edward62740/WMNS/Software Files/nrf_firmware/docu/meshnetwork.jpg

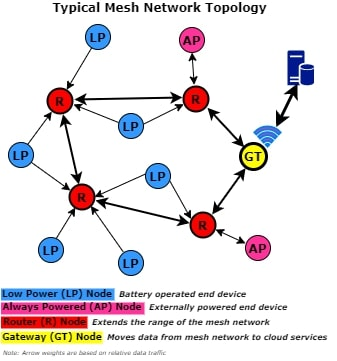
Software Files/nrf_firmware/docu/meshnetwork.jpg
