edward62740/WMNS/PCB Files/Debugger/Debugger.brd

## EAGLE design PCB Files/Debugger/Debugger.brd (2022-01-03)

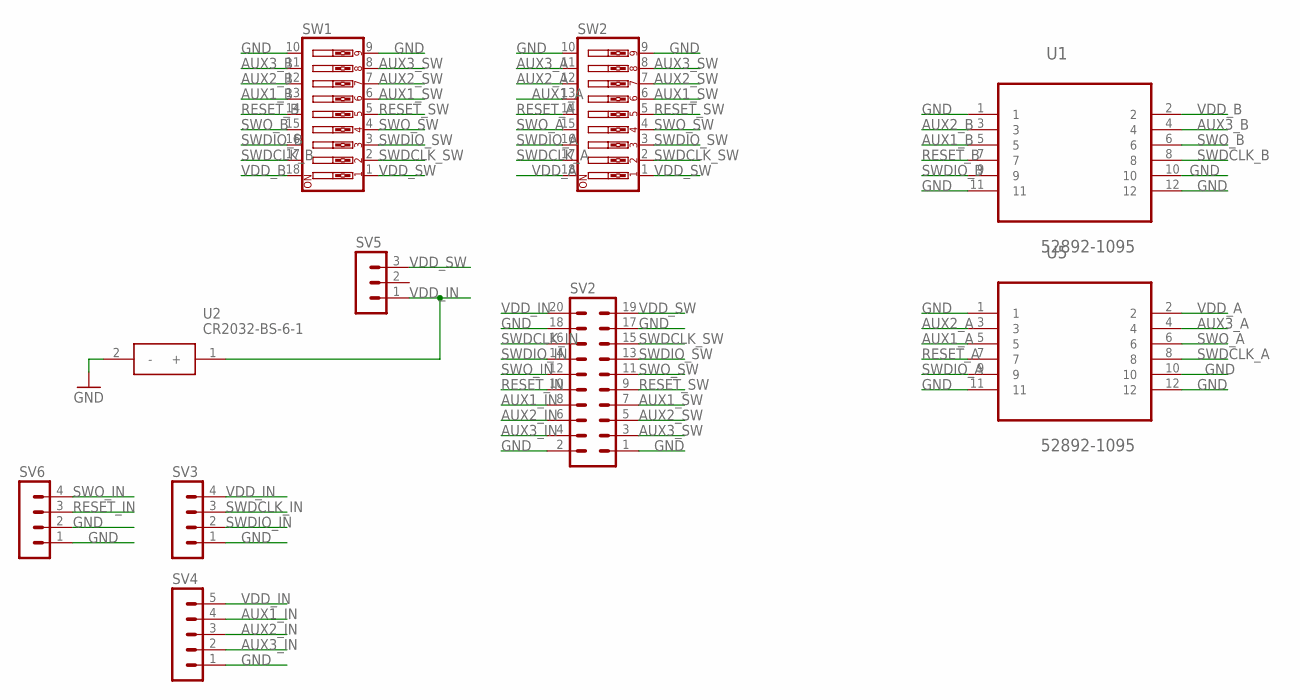
[picture p53: schematic Debugger.sch]

Parts:
SV2: MA10-2
SV3, SV6: MA04-1
SV4: MA05-1
SV5: MA03-1
SW1, SW2: SW_DIP-9; EDG-09
U1, U5: 52892-1095; MOLEX_52892-1095
U2: CR2032-BS-6-1; CR2032BS61

Connections:
AUX1_A: SW2.13, U5.5
AUX1_B: SW1.13, U1.5
AUX1_IN: SV2.8, SV4.4
AUX1_SW: SV2.7, SW1.6, SW2.6
AUX2_A: SW2.12, U5.3
AUX2_B: SW1.12, U1.3
AUX2_IN: SV2.6, SV4.3
AUX2_SW: SV2.5, SW1.7, SW2.7
AUX3_A: SW2.11, U5.4
AUX3_B: SW1.11, U1.4
AUX3_IN: SV2.4, SV4.2
AUX3_SW: SV2.3, SW1.8, SW2.8
GND: SV2.1, SV2.2, SV2.17, SV2.18, SV3.1, SV4.1, SV6.1, SV6.2, SW1.9, SW1.10, SW2.9, SW2.10, U1.1, U1.10, U1.11, U1.12, U2.2 (-), U5.1, U5.10, U5.11, U5.12
RESET_A: SW2.14, U5.7
RESET_B: SW1.14, U1.7
RESET_IN: SV2.10, SV6.3
RESET_SW: SV2.9, SW1.5, SW2.5
SWDCLK_A: SW2.17, U5.8
SWDCLK_B: SW1.17, U1.8
SWDCLK_IN: SV2.16, SV3.3
SWDCLK_SW: SV2.15, SW1.2, SW2.2
SWDIO_A: SW2.16, U5.9
SWDIO_B: SW1.16, U1.9
SWDIO_IN: SV2.14, SV3.2
SWDIO_SW: SV2.13, SW1.3, SW2.3
SWO_A: SW2.15, U5.6
SWO_B: SW1.15, U1.6
SWO_IN: SV2.12, SV6.4
SWO_SW: SV2.11, SW1.4, SW2.4
VDD_A: SW2.18, U5.2
VDD_B: SW1.18, U1.2
VDD_IN: SV2.20, SV3.4, SV4.5, SV5.1, U2.1 (+)
VDD_SW: SV2.19, SV5.3, SW1.1, SW2.1

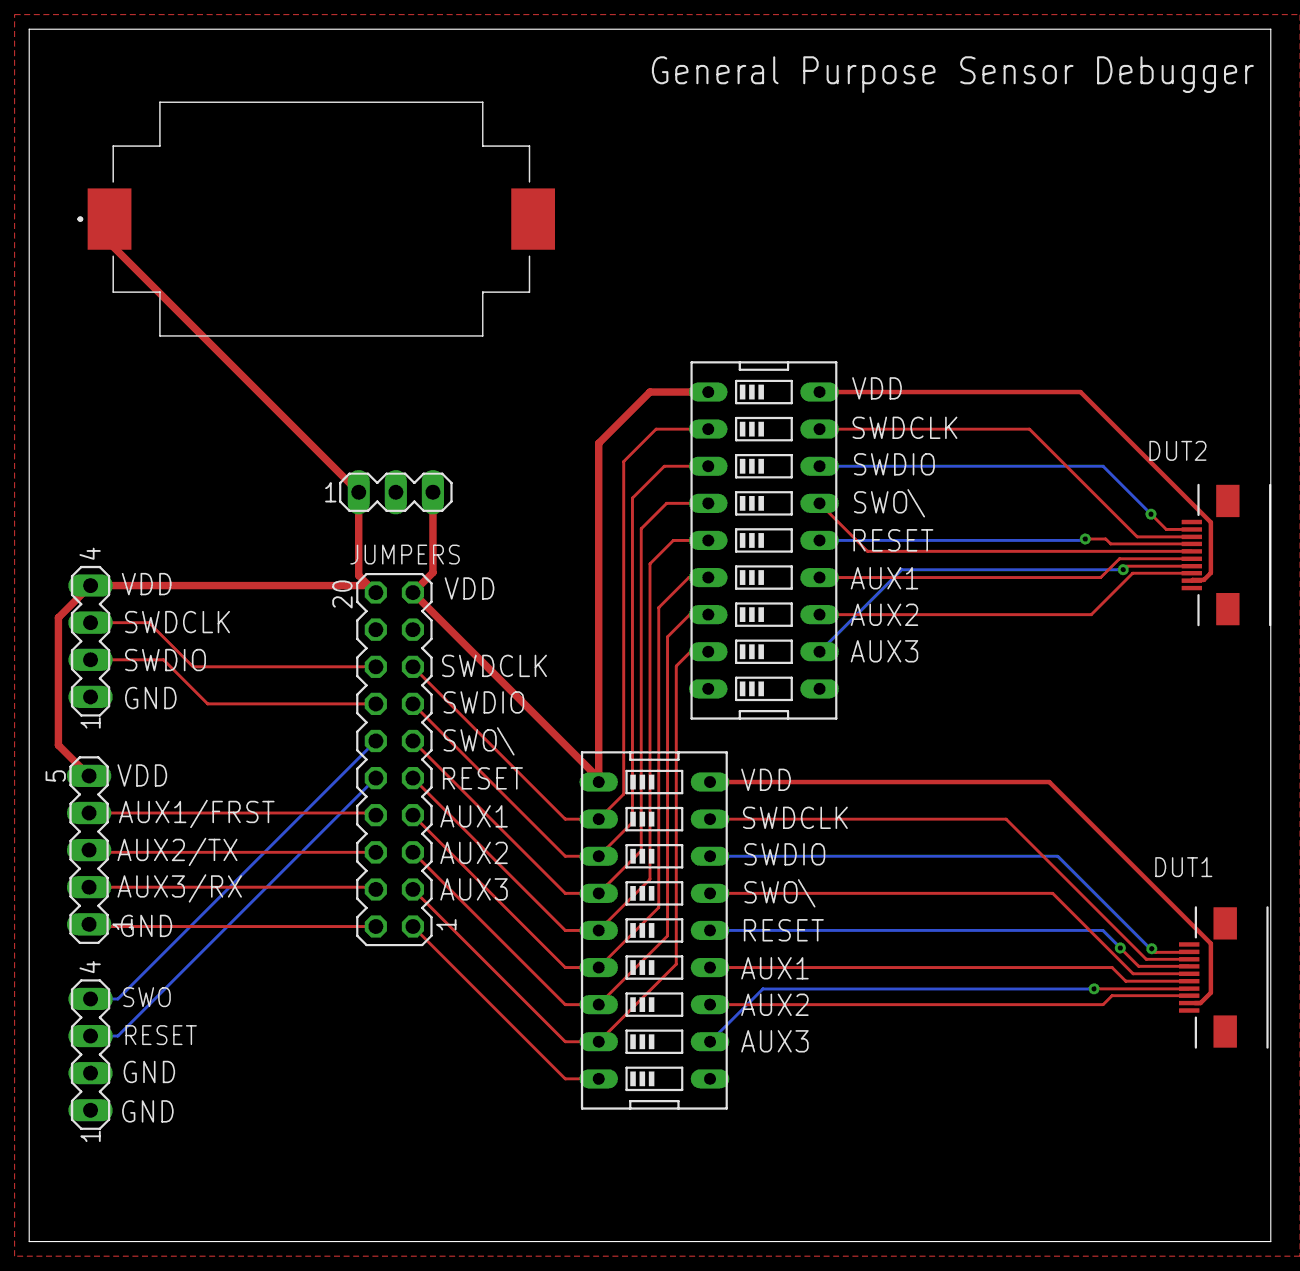
[picture p54: board Debugger.brd from above]

Board: 2 copper layers, 85.0 x 83.0 mm, 10 parts (0 on the bottom side), 33 nets.
