edward62740/WMNS/PCB Files/Gateway/Gateway v2.brd

## EAGLE design PCB Files/Gateway/Gateway v2.brd (2022-01-03)

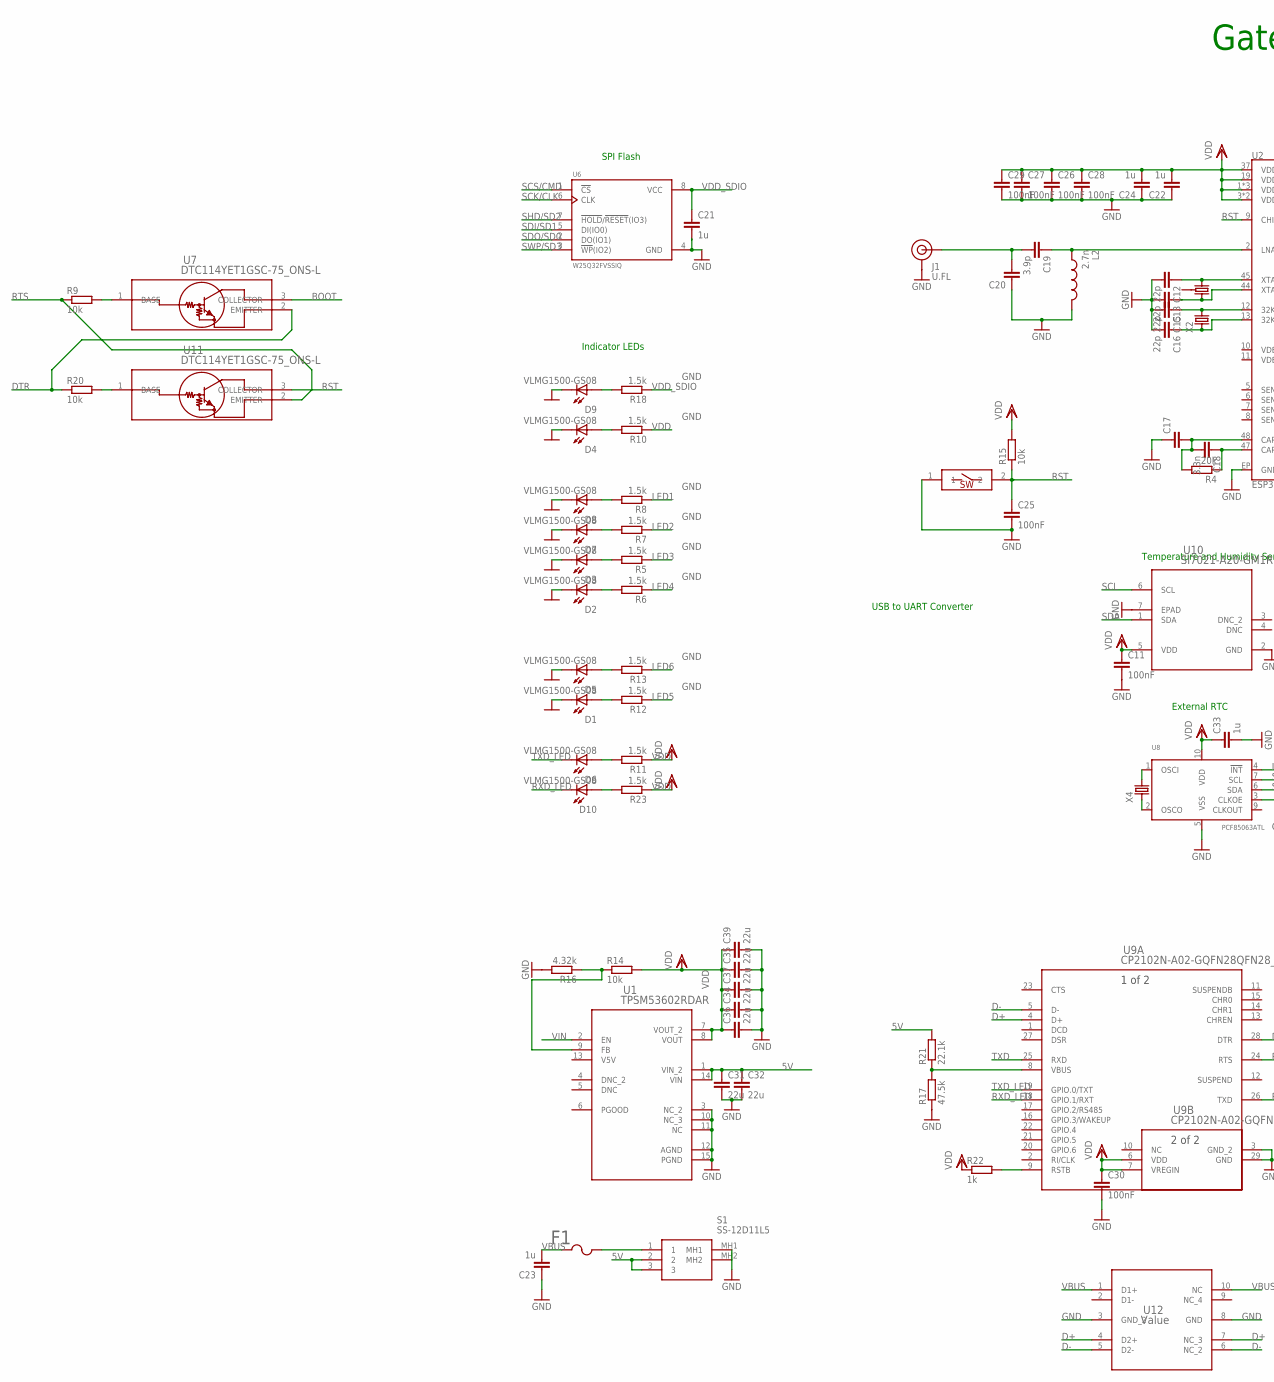
[picture p55: schematic Gateway v2.sch, part in row 1, column 1]

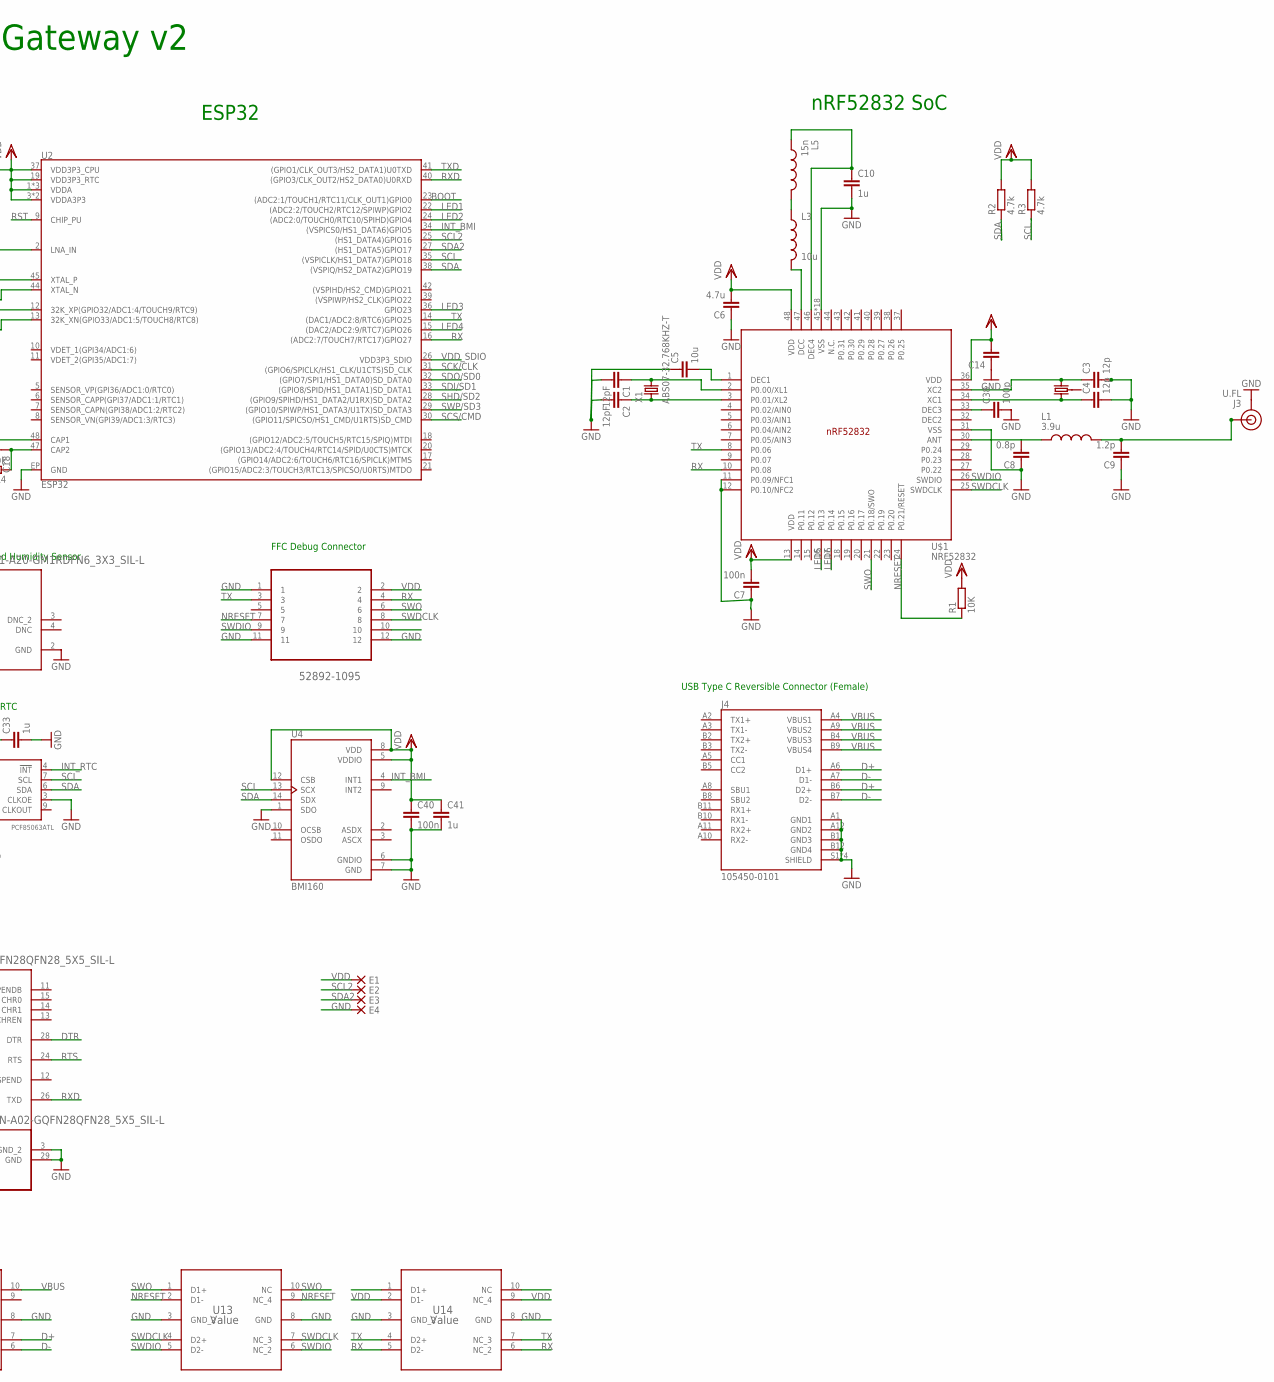
[picture p56: schematic Gateway v2.sch, part in row 1, column 2]

Parts:
C1, C2: 12pF; C0402
C3, C4: 12p; C0402
C5: 10u; C0402
C6: 4.7u; C0402
C7, C40: 100n; C0402
C8: 0.8p; C0402
C9: 1.2p; C0402
C10, C21, C41: 1u; C0402
C11, C25, C26, C27, C28, C29, C30: 100nF; C0402
C12, C13, C15, C16: 22p; C0402
C14: 100u; C0402
C17: 10n; C0402
C18: 3.3n; C0402
C19: 3.9p; C0402
C20: 2.4p; C0402
C22, C23, C24, C33: 1u; C0603R
C31, C32, C34, C35, C36, C37, C39: 22u; C0603R
C38: 100p; C0402
D1, D2, D3, D4, D5, D6, D7, D8, D9, D10: VLMG1500-GS08; LEDC1005X35N
E1, E2, E3, E4: DPADS_PAD-0400-S; DPADS_0400-S
F1: 1210L050YR1210LSERIES_LTF-L; 1210LSERIES_LTF-L
J1, J3: U.FL
J4: 105450-0101; MOLEX_105450-0101
L1: 3.9u; INDC0402X26N
L2: 2.7n; INDC0402X26N
L3: 10u; L0603
L5: 15n; INDC0402X26N
R1: 10K; R0402
R2, R3: 4.7k; R0402
R4: 20k; R0402
R5, R6, R7, R8, R10, R11, R12, R13, R18, R23: 1.5k; R0402
R9, R14, R15, R20: 10k; R0402
R16: 4.32k; R0402
R17: 47.5k; R0402
R21: 22.1k; R0402
R22: 1k; R0402
RESET: SMDSWITCH; RESC4217X170
S1: SS-12D11L5; SS12D11L5
U1: TPSM53602RDAR; B3QFN15_RDA_TEX
U2: ESP32; QFN48-0.4MM
U4: BMI160; PQFN50P300X250X88-14N
U5: 52892-1095; MOLEX_52892-1095
U6: W25Q32FVSSIQ; SOIC127P790X216-8N
U7, U11: DTC114YET1GSC-75_ONS-L; SC-75_ONS-L
U8: PCF85063ATL; SOT1197-1
U9: CP2102N-A02-GQFN28QFN28_5X5_SIL-L; QFN28_5X5_SIL-L
U10: SI7021-A20-GM1RDFN6_3X3_SIL-L; DFN6_3X3_SIL-L
U12, U13, U14: Value; DQA0010A
U$1: NRF52832; QFN40P600X600X90-48_N
X1, X2, X4: ABS07-32.768KHZ-T
Y1, Y2: CRYSTAL-26MHZSMD-3.2X2.5; CRYSTAL-SMD-3.2X2.5MM

Connections:
5V: C31.1, C32.1, R21.2, S1.2, S1.3, U1.1 (VIN_2), U1.14 (VIN)
BOOT: U2.23 ((ADC2:1/TOUCH1/RTC11/CLK_OUT1)GPIO0), U7.3 (COLLECTOR)
D+: J4.A6 (D1+), J4.B6 (D2+), U9.4 (D+), U12.4 (D2+), U12.7 (NC_3)
D-: J4.A7 (D1-), J4.B7 (D2-), U9.5 (D-), U12.5 (D2-), U12.6 (NC_2)
DTR: R20.1, U7.2 (EMITTER), U9.28 (DTR)
GND: C1.2, C2.2, C3.2, C4.2, C5.1, C6.1, C7.1, C8.1, C9.1, C10.2, C11.2, C12.2, C13.2, C14.1, C15.2, C16.2, C17.1, C20.1, C21.2, C22.1, C23.1, C24.1, C25.2, C26.2, C27.2, C28.2, C29.2, C30.2, C31.2, C32.2, C33.2, C34.2, C35.2, C36.2, C37.2, C38.2, C39.2, C40.2, C41.2, D1.2, D2.2, D3.2, D4.2, D5.2, D7.2, D8.2, D9.2, E4.PAD, J1.1 (GND), J1.2 (GND), J3.1 (GND), J3.2 (GND), J4.A1 (GND1), J4.A12 (GND2), J4.B1 (GND3), J4.B12 (GND4), J4.S1 (SHIELD), J4.S2 (SHIELD), J4.S3 (SHIELD), J4.S4 (SHIELD), L2.2, R16.2, R17.1, RESET.1, S1.MH1, S1.MH2, U1.3 (NC_2), U1.10 (NC_3), U1.11 (NC), U1.12 (AGND), U1.15 (PGND), U2.EP (GND), U4.1 (SDO), U4.6 (GNDIO), U4.7 (GND), U5.1, U5.11, U5.12, U6.4 (GND), U8.3 (CLKOE), U8.5 (VSS), U9.3 (GND_2), U9.29 (GND), U10.2 (GND), U10.7 (EPAD), U12.3 (GND_2), U12.8 (GND), U13.3 (GND_2), U13.8 (GND), U14.3 (GND_2), U14.8 (GND), U$1.11 (P0.09/NFC1), U$1.12 (P0.10/NFC2), U$1.31 (VSS), U$1.45 (VSS), U$1.PAD (VSS), U$1.PAD@VIA01 (VSS), U$1.PAD@VIA02 (VSS), U$1.PAD@VIA03 (VSS), U$1.PAD@VIA04 (VSS), U$1.PAD@VIA05 (VSS), U$1.PAD@VIA06 (VSS), U$1.PAD@VIA07 (VSS), U$1.PAD@VIA08 (VSS), U$1.PAD@VIA09 (VSS), U$1.PAD@VIA10 (VSS), U$1.PAD@VIA11 (VSS), U$1.PAD@VIA12 (VSS), U$1.PAD@VIA13 (VSS), U$1.PAD@VIA14 (VSS), U$1.PAD@VIA15 (VSS), U$1.PAD@VIA16 (VSS)
INT_BMI: U2.34 ((VSPICS0/HS1_DATA6)GPIO5), U4.4 (INT1)
INT_RTC: U8.4 (!INT!)
LED1: R8.1, U2.22 ((ADC2:2/TOUCH2/RTC12/SPIWP)GPIO2)
LED2: R7.1, U2.24 ((ADC2:0/TOUCH0/RTC10/SPIHD)GPIO4)
LED3: R5.1, U2.36 (GPIO23)
LED4: R6.1, U2.15 ((DAC2/ADC2:9/RTC7)GPIO26)
LED5: R12.1, U$1.16 (P0.13)
LED6: R13.1, U$1.17 (P0.14)
unnamed: C1.1, U$1.2 (P0.00/XL1), X1.2
unnamed: C2.1, U$1.3 (P0.01/XL2), X1.1
unnamed: C3.1, U$1.35 (XC2), Y1.3 (2)
unnamed: C4.1, U$1.34 (XC1), Y1.1
unnamed: C5.2, U$1.1 (DEC1)
unnamed: C8.2, L1.1, U$1.30 (ANT)
unnamed: C13.1, U2.44 (XTAL_N), Y2.3 (2)
unnamed: C12.1, U2.45 (XTAL_P), Y2.1
unnamed: L3.2, U$1.47 (DCC)
unnamed: L3.1, L5.2
unnamed: C10.1, L5.1, U$1.46 (DEC4)
unnamed: C15.1, U2.12 (32K_XP(GPIO32/ADC1:4/TOUCH9/RTC9)), X2.2
unnamed: C16.1, U2.13 (32K_XN(GPIO33/ADC1:5/TOUCH8/RTC8)), X2.1
unnamed: C18.1, R4.1, U2.47 (CAP2)
unnamed: C38.1, U$1.33 (DEC3)
unnamed: C17.2, C18.2, R4.2, U2.48 (CAP1)
unnamed: D3.1, R5.2
unnamed: D7.1, R7.2
unnamed: D8.1, R8.2
unnamed: C19.1, L2.1, U2.2 (LNA_IN)
unnamed: R17.2, R21.1, U9.8 (VBUS)
unnamed: D2.1, R6.2
unnamed: D4.1, R10.2
unnamed: D1.1, R12.2
unnamed: D5.1, R13.2
unnamed: C19.2, C20.2, J1.FEED (SIGNAL)
unnamed: R20.2, U11.1 (BASE)
unnamed: R9.2, U7.1 (BASE)
unnamed: D9.1, R18.2
unnamed: R14.1, R16.1, U1.9 (FB)
unnamed: U8.1 (OSCI), X4.2
unnamed: U8.2 (OSCO), X4.1
unnamed: R22.2, U9.9 (RSTB)
unnamed: D6.1, R11.2
unnamed: D10.1, R23.2
unnamed: F1.2, S1.1
NRESET: R1.1, U5.7, U13.2 (D1-), U13.9 (NC_4), U$1.24 (P0.21/RESET)
RFP1: C9.2, J3.FEED (SIGNAL), L1.2
RST: C25.1, R15.1, RESET.2, U2.9 (CHIP_PU), U11.3 (COLLECTOR)
RTS: R9.1, U9.24 (RTS), U11.2 (EMITTER)
RX: U2.16 ((ADC2:7/TOUCH7/RTC17)GPIO27), U5.4, U14.5 (D2-), U14.6 (NC_2), U$1.10 (P0.08)
RXD: U2.40 ((GPIO3/CLK_OUT2/HS2_DATA0)U0RXD), U9.26 (TXD)
RXD_LED: D10.2, U9.18 (GPIO.1/RXT)
SCK/CLK: U2.31 ((GPIO6/SPICLK/HS1_CLK/U1CTS)SD_CLK), U6.6 (CLK)
SCL: R3.1, U2.35 ((VSPICLK/HS1_DATA7)GPIO18), U4.13 (SCX), U8.7 (SCL), U10.6 (SCL)
SCL2: E2.PAD, U2.25 ((HS1_DATA4)GPIO16)
SCS/CMD: U2.30 ((GPIO11/SPICSO/HS1_CMD/U1RTS)SD_CMD), U6.1 (!CS)
SDA: R2.1, U2.38 ((VSPIQ/HS2_DATA2)GPIO19), U4.14 (SDX), U8.6 (SDA), U10.1 (SDA)
SDA2: E3.PAD, U2.27 ((HS1_DATA5)GPIO17)
SDI/SD1: U2.33 ((GPIO8/SPID/HS1_DATA1)SD_DATA1), U6.5 (DI(IO0))
SDO/SD0: U2.32 ((GPIO7/SPI1/HS1_DATA0)SD_DATA0), U6.2 (DO(IO1))
SHD/SD2: U2.28 ((GPIO9/SPIHD/HS1_DATA2/U1RX)SD_DATA2), U6.7 (!HOLD!/!RESET!(IO3))
SWDCLK: U5.8, U13.4 (D2+), U13.7 (NC_3), U$1.25 (SWDCLK)
SWDCLK1: U14.1 (D1+)
SWDIO: U5.9, U13.5 (D2-), U13.6 (NC_2), U$1.26 (SWDIO)
SWO: U5.6, U13.1 (D1+), U13.10 (NC), U$1.21 (P0.18/SWO)
SWP/SD3: U2.29 ((GPIO10/SPIWP/HS1_DATA3/U1TX)SD_DATA3), U6.3 (!WP!(IO2))
TX: U2.14 ((DAC1/ADC2:8/RTC6)GPIO25), U5.3, U14.4 (D2+), U14.7 (NC_3), U$1.8 (P0.06)
TXD: U2.41 ((GPIO1/CLK_OUT3/HS2_DATA1)U0TXD), U9.25 (RXD)
TXD_LED: D6.2, U9.19 (GPIO.0/TXT)
VBUS: C23.2, F1.1, J4.A4 (VBUS1), J4.A9 (VBUS2), J4.B4 (VBUS3), J4.B9 (VBUS4), U12.1 (D1+), U12.10 (NC)
VDD: C6.2, C7.2, C11.1, C14.2, C22.2, C24.2, C26.1, C27.1, C28.1, C29.1, C30.1, C33.1, C34.1, C35.1, C36.1, C37.1, C39.1, C40.1, C41.1, E1.PAD, R1.2, R2.2, R3.2, R10.1, R11.1, R14.2, R15.2, R22.1, R23.1, U1.7 (VOUT_2), U1.8 (VOUT), U2.1 (VDDA), U2.3 (VDDA3P3), U2.4 (VDDA3P3), U2.19 (VDD3P3_RTC), U2.37 (VDD3P3_CPU), U2.43 (VDDA), U2.46 (VDDA), U4.5 (VDDIO), U4.8 (VDD), U4.12 (CSB), U5.2, U8.10 (VDD), U9.6 (VDD), U9.7 (VREGIN), U10.5 (VDD), U14.2 (D1-), U14.9 (NC_4), U$1.13 (VDD), U$1.36 (VDD), U$1.48 (VDD)
VDD_SDIO: C21.1, R18.1, U2.26 (VDD3P3_SDIO), U6.8 (VCC)
VIN: U1.2 (EN)

Notes on the sheet:
Indicator LEDs
SPI Flash
USB to UART Converter
External RTC
Temperature and Humidity Sensor
FFC Debug Connector
USB Type C Reversible Connector (Female)
nRF52832 SoC
ESP32
Gateway v2

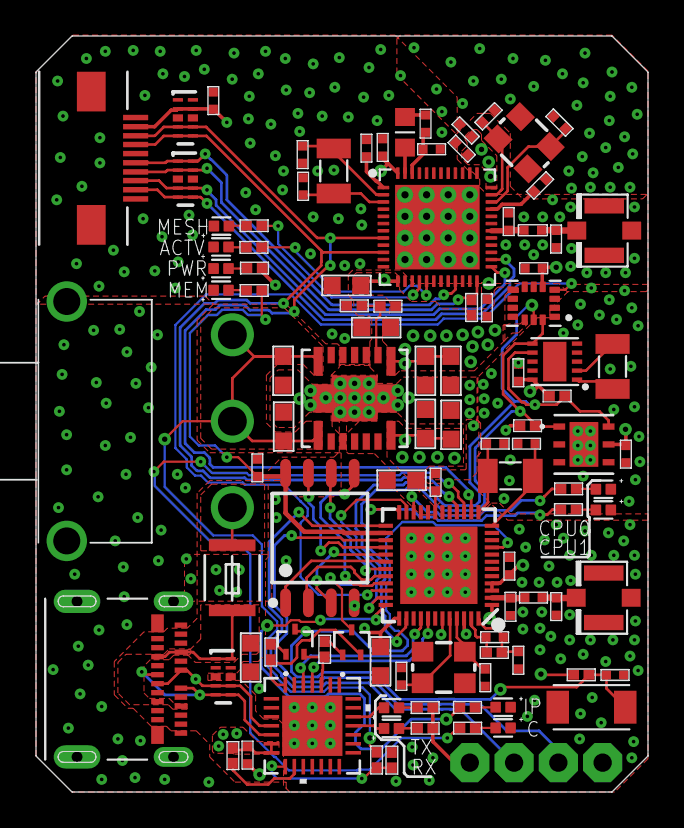
[picture p57: board Gateway v2.brd from above]

Board: 4 copper layers, 34.0 x 42.0 mm, 106 parts (0 on the bottom side), 75 nets.
