edward62740/WMNS/PCB Files/CO2SN/CO2SN v2.brd

## EAGLE design PCB Files/CO2SN/CO2SN v2.brd (2022-01-03)

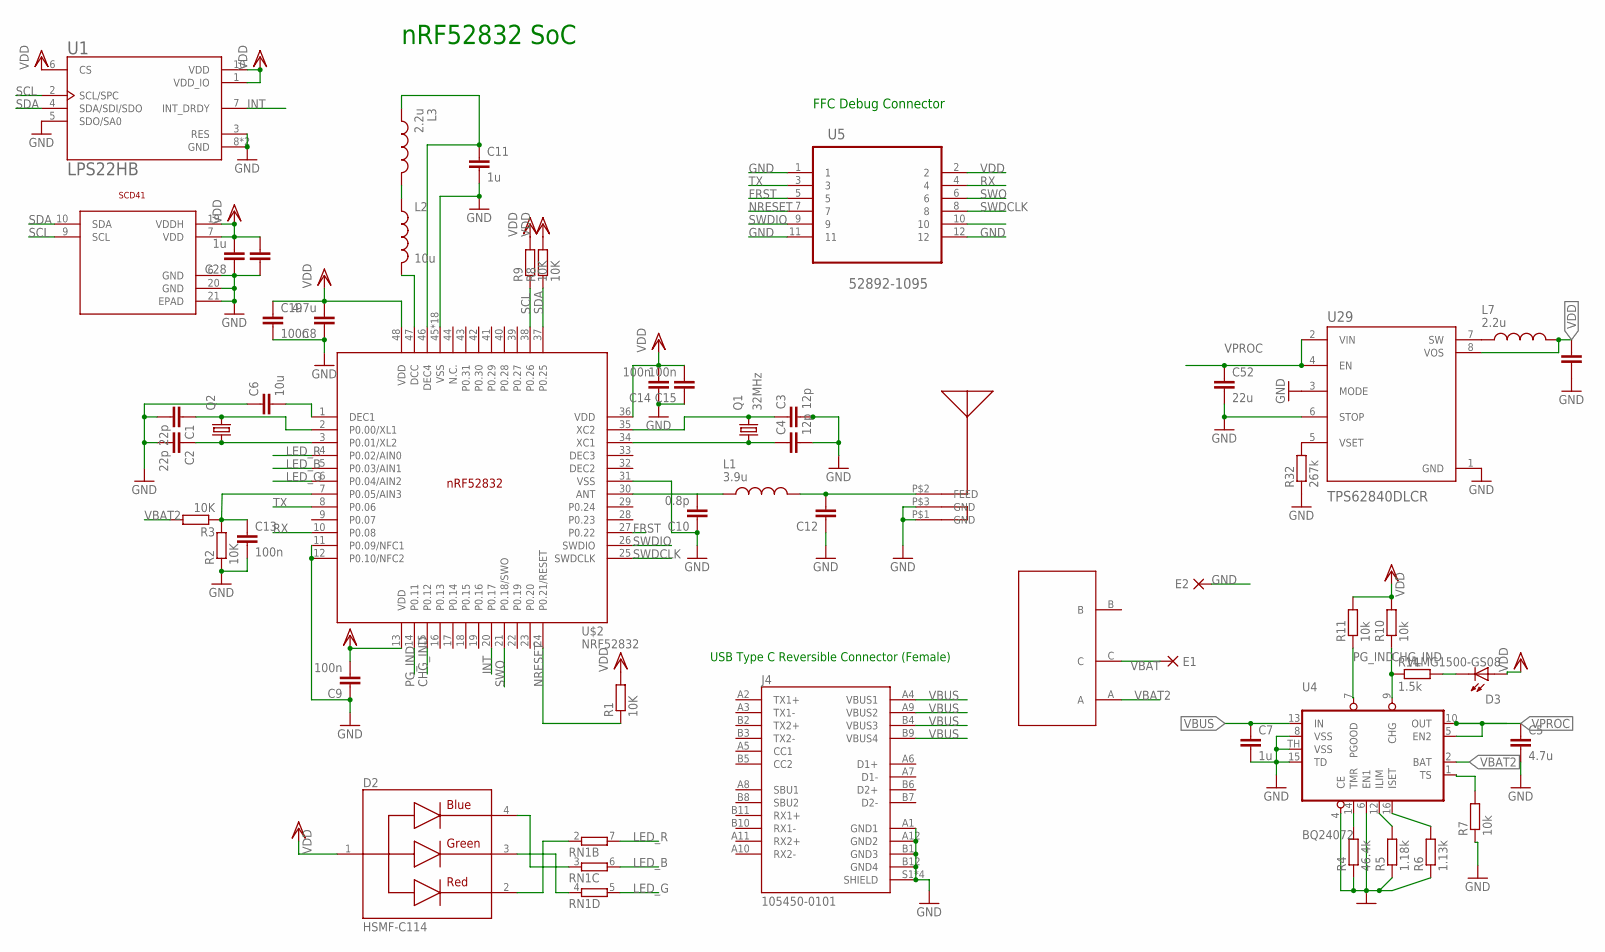
[picture p58: schematic CO2SN v2.sch]

Parts:
C1, C2: 22p; C0402
C3, C4: 12p; C0402
C5, C8: 4.7u; C0402
C6: 10u; C0402
C7, C11, C28: 1u; C0402
C9: 100n; C0603R
C10: 0.8p; C0402
C12: 1.2p; C0402
C13, C14, C15, C19: 100n; C0402
C29, C52, C58: 22u; C0603R
D2: HSMF-C114; DIOSC160X150X35-4N
D3: VLMG1500-GS08; LEDC1005X35N
E1, E2: DPADS_PAD-0400-S; DPADS_0400-S
J4: 105450-0101; MOLEX_105450-0101
L1: 3.9u; INDC0402X26N
L2: 10u; L0603
L3: 2.2u; INDC0402X26N
L7: 2.2u; INDC3225X120N
Q1: 32MHz; 2.0X1.6_KX-5
Q2: KX-327-RT; 2.0X1.2
R1, R2, R3, R8, R9: 10K; R0402
R4: 46.4k; R0402
R5: 1.18k; R0402
R6: 1.13k; R0402
R7, R10, R11: 10k; R0402
R14: 1.5k; R0402
R32: 267k; R0402
RN1: 4R-N0402ARV341; 4X0402ARV341
U1: LPS22HB; LGA10R50P2X3_200X200X80
U4: BQ24072; S-PVQFN-N16
U5: 52892-1095; MOLEX_52892-1095
U29: TPS62840DLCR; SON50P200X150X100-8N
U$1: SCD41
U$2: NRF52832; QFN40P600X600X90-48_N
U$3: SMDTOGGLESWITCH
U$4: CHIPANTENNAL2

Connections:
CHG_IND: R10.1, R14.1, U4.9 (CHG), U$2.15 (P0.12)
FRST: U5.5, U$2.27 (P0.22)
GND: C1.2, C2.2, C3.2, C4.2, C5.2, C6.1, C7.2, C8.1, C9.1, C10.1, C11.2, C12.1, C13.2, C14.1, C15.1, C19.2, C28.1, C29.2, C52.2, C58.2, E2.PAD, J4.A1 (GND1), J4.A12 (GND2), J4.B1 (GND3), J4.B12 (GND4), J4.S1 (SHIELD), J4.S2 (SHIELD), J4.S3 (SHIELD), J4.S4 (SHIELD), R2.1, R4.1, R5.1, R6.1, R7.1, R32.1, U1.3 (RES), U1.5 (SDO/SA0), U1.8 (GND), U1.9 (GND), U4.4 (CE), U4.6 (EN1), U4.8 (VSS), U4.15 (TD), U4.TH (VSS), U5.1, U5.11, U5.12, U29.1 (GND), U29.3 (MODE), U29.6 (STOP), U$1.6 (GND), U$1.20 (GND), U$1.21 (EPAD), U$2.11 (P0.09/NFC1), U$2.12 (P0.10/NFC2), U$2.31 (VSS), U$2.45 (VSS), U$2.PAD (VSS), U$2.PAD@VIA01 (VSS), U$2.PAD@VIA02 (VSS), U$2.PAD@VIA03 (VSS), U$2.PAD@VIA04 (VSS), U$2.PAD@VIA05 (VSS), U$2.PAD@VIA06 (VSS), U$2.PAD@VIA07 (VSS), U$2.PAD@VIA08 (VSS), U$2.PAD@VIA09 (VSS), U$2.PAD@VIA10 (VSS), U$2.PAD@VIA11 (VSS), U$2.PAD@VIA12 (VSS), U$2.PAD@VIA13 (VSS), U$2.PAD@VIA14 (VSS), U$2.PAD@VIA15 (VSS), U$2.PAD@VIA16 (VSS), U$4.P$1 (GND), U$4.P$3 (GND)
INT: U1.7 (INT_DRDY), U$2.20 (P0.17)
LED_B: RN1.6 (2), U$2.5 (P0.03/AIN1)
LED_G: RN1.5 (2), U$2.6 (P0.04/AIN2)
LED_R: RN1.7 (2), U$2.4 (P0.02/AIN0)
unnamed: C1.1, Q2.2, U$2.2 (P0.00/XL1)
unnamed: C2.1, Q2.1, U$2.3 (P0.01/XL2)
unnamed: C3.1, Q1.3 (2), U$2.35 (XC2)
unnamed: C4.1, Q1.1, U$2.34 (XC1)
unnamed: L2.2, U$2.47 (DCC)
unnamed: C10.2, L1.1, U$2.30 (ANT)
unnamed: C6.2, U$2.1 (DEC1)
unnamed: R4.2, U4.14 (TMR)
unnamed: R5.2, U4.12 (ILIM)
unnamed: L2.1, L3.2
unnamed: C11.1, L3.1, U$2.46 (DEC4)
unnamed: R6.2, U4.16 (ISET)
unnamed: D2.2, RN1.2 (1)
unnamed: D3.2, R14.2
unnamed: C13.1, R2.2, R3.1, U$2.7 (P0.05/AIN3)
unnamed: D2.3, RN1.4 (1)
unnamed: D2.4, RN1.3 (1)
unnamed: L7.1, U29.7 (SW)
unnamed: R32.2, U29.5 (VSET)
NRESET: R1.1, U5.7, U$2.24 (P0.21/RESET)
PG_IND: R11.1, U4.7 (PGOOD), U$2.14 (P0.11)
RF: C12.2, L1.2, U$4.P$2 (FEED)
RX: U5.4, U$2.10 (P0.08)
SCL: R9.1, U1.2 (SCL/SPC), U$1.9 (SCL), U$2.38 (P0.26)
SDA: R8.1, U1.4 (SDA/SDI/SDO), U$1.10 (SDA), U$2.37 (P0.25)
SWDCLK: U5.8, U$2.25 (SWDCLK)
SWDIO: U5.9, U$2.26 (SWDIO)
SWO: U5.6, U$2.21 (P0.18/SWO)
TS: R7.2, U4.1 (TS)
TX: U5.3, U$2.8 (P0.06)
VBAT: E1.PAD, U$3.C
VBAT2: R3.2, U4.2 (BAT), U$3.A
VBUS: C7.1, J4.A4 (VBUS1), J4.A9 (VBUS2), J4.B4 (VBUS3), J4.B9 (VBUS4), U4.13 (IN)
VDD: C8.2, C9.2, C14.2, C15.2, C19.1, C28.2, C29.1, C58.1, D2.1, D3.1, L7.2, R1.2, R8.2, R9.2, R10.2, R11.2, U1.1 (VDD_IO), U1.6 (CS), U1.10 (VDD), U5.2, U29.8 (VOS), U$1.7 (VDD), U$1.19 (VDDH), U$2.13 (VDD), U$2.36 (VDD), U$2.48 (VDD)
VPROC: C5.1, C52.1, U4.5 (EN2), U4.10 (OUT), U29.2 (VIN), U29.4 (EN)

Notes on the sheet:
nRF52832 SoC
USB Type C Reversible Connector (Female)
FFC Debug Connector

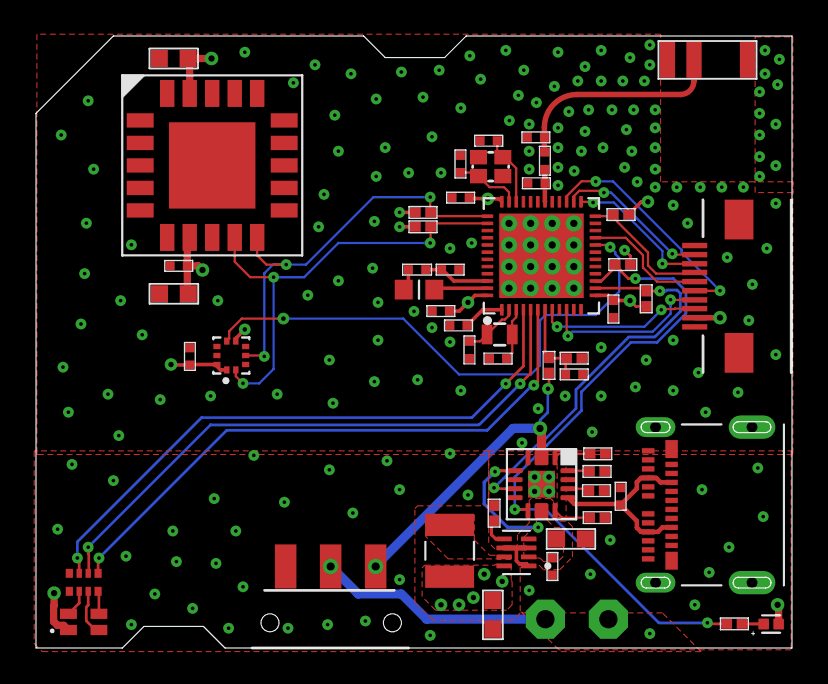
[picture p59: board CO2SN v2.brd from above]

Board: 4 copper layers, 42.0 x 34.0 mm, 53 parts (0 on the bottom side), 42 nets.
