edward62740/WMNS/Software Files/nrf_firmware/common/drivers/SCD41_API/sensirion_i2c_hal.c

/*
 * Copyright (c) 2018, Sensirion AG
 * All rights reserved.
 *
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
 * * Neither the name of Sensirion AG nor the names of its
 *   contributors may be used to endorse or promote products derived from
 *   this software without specific prior written permission.
 *
 * THIS SOFTWARE IS PROVIDED BY THE COPYRIGHT HOLDERS AND CONTRIBUTORS "AS IS"
 * AND ANY EXPRESS OR IMPLIED WARRANTIES, INCLUDING, BUT NOT LIMITED TO, THE
 * IMPLIED WARRANTIES OF MERCHANTABILITY AND FITNESS FOR A PARTICULAR PURPOSE
 * ARE DISCLAIMED. IN NO EVENT SHALL THE COPYRIGHT HOLDER OR CONTRIBUTORS BE
 * LIABLE FOR ANY DIRECT, INDIRECT, INCIDENTAL, SPECIAL, EXEMPLARY, OR
 * CONSEQUENTIAL DAMAGES (INCLUDING, BUT NOT LIMITED TO, PROCUREMENT OF
 * SUBSTITUTE GOODS OR SERVICES; LOSS OF USE, DATA, OR PROFITS; OR BUSINESS
 * INTERRUPTION) HOWEVER CAUSED AND ON ANY THEORY OF LIABILITY, WHETHER IN
 * CONTRACT, STRICT LIABILITY, OR TORT (INCLUDING NEGLIGENCE OR OTHERWISE)
 * ARISING IN ANY WAY OUT OF THE USE OF THIS SOFTWARE, EVEN IF ADVISED OF THE
 * POSSIBILITY OF SUCH DAMAGE.
 */

#include <nrf_delay.h>
#include <nrf_drv_twi.h>
#include <stdio.h>

#include "sensirion_common.h"
#include "sensirion_config.h"
#include "sensirion_i2c_hal.h"
#include "nrf_drv_twi.h"
#include "nrf_gpio.h"

/**
 * Nordic specific configuration. Change the pin numbers if you use other pins
 * than defined below.
 */



/**
 * Create new TWI instance. You may also use a different interface. In this
 * case, please adapt the code below.
 */
static const nrf_drv_twi_t *p_twi = NULL;
/**
 * Initialize all hard- and software components that are needed for the I2C
 * communication.
 */
void sensirion_i2c_hal_init(const nrf_drv_twi_t *l_twi)
{

    p_twi = l_twi;
    return;
}

/**
 * Release all resources initialized by sensirion_i2c_hal_init().
 */
void sensirion_i2c_hal_free(void)
{
}

/**
 * Execute one read transaction on the I2C bus, reading a given number of bytes.
 * If the device does not acknowledge the read command, an error shall be
 * returned.
 *
 * @param address 7-bit I2C address to read from
 * @param data    pointer to the buffer where the data is to be stored
 * @param count   number of bytes to read from I2C and store in the buffer
 * @returns 0 on success, error code otherwise
 *
 * error codes:  3 -> error detected by hardware (internal error)
 *              17 -> driver not ready for new transfer (busy)
 */
int8_t sensirion_i2c_hal_read(uint8_t address, uint8_t* data, uint16_t count)
{
    int8_t err = nrf_drv_twi_rx(p_twi, address, data, (uint8_t)count);
    return err;
}

/**
 * Execute one write transaction on the I2C bus, sending a given number of
 * bytes. The bytes in the supplied buffer must be sent to the given address. If
 * the slave device does not acknowledge any of the bytes, an error shall be
 * returned.
 *
 * @param address 7-bit I2C address to write to
 * @param data    pointer to the buffer containing the data to write
 * @param count   number of bytes to read from the buffer and send over I2C
 * @returns 0 on success, error code otherwise
 *
 * error codes:  3 -> error detected by hardware (internal error)
 *              17 -> driver not ready for new transfer (busy)
 */
int8_t sensirion_i2c_hal_write(uint8_t address, const uint8_t* data,
                               uint16_t count)
{
    int8_t err =
        nrf_drv_twi_tx(p_twi, address, data, (uint8_t)count, false);
    return err;
}

/**
 * Sleep for a given number of microseconds. The function should delay the
 * execution for at least the given time, but may also sleep longer.
 *
 * @param useconds the sleep time in microseconds
 */
void sensirion_i2c_hal_sleep_usec(uint32_t useconds)
{


    nrf_gpio_cfg_output(2);
    nrf_gpio_cfg_output(3);
    nrf_gpio_cfg_output(4);
    int led = 2;
    while(useconds >= 50000)
    {
        nrf_gpio_pin_toggle(led);
        nrf_delay_us(50000);
        useconds -= 50000;
        if(led == 4) {
            led = 1;
        }
        led++;
    }
    nrf_gpio_cfg_default(2);
    nrf_gpio_cfg_default(3);
    nrf_gpio_cfg_default(4);
    nrf_delay_us(useconds);


}
