edward62740/WMNS/Software Files/nrf_firmware/common/drivers/veml6030.c

#include "nrf_drv_twi.h"
#include "nrf_delay.h"
#include "nrf_log.h"
#include "veml6030.h"
#include "math.h"

static const uint8_t address = 0x48;
static const nrf_drv_twi_t *p_twi = NULL;

const float IT800[4] = { .0036, .0072, .0288, .0576 };
const float IT400[4] = { .0072, .0144, .0576, .1152 };
const float IT200[4] = { .0144, .0288, .1152, .2304 };
const float IT100[4] = { .0288, .0576, .2304, .4608 };
const float IT50[4] = { .0576, .1152, .4608, .9216 };
const float IT25[4] = { .1152, .2304, .9216, 1.8432 };


uint8_t veml6030_write_reg(uint8_t reg, uint16_t value)
{
    uint8_t res[3];
    res[0] = reg;
    res[1] = value ;
    res[2] = value >> 8 ;

    ret_code_t err_code;
    err_code = nrf_drv_twi_tx(p_twi, address, res, 3, false);
    APP_ERROR_CHECK(err_code);
    return 0;
}

uint16_t veml6030_read_reg(uint8_t reg)
{
    uint8_t res[2];

    ret_code_t err_code;
    err_code = nrf_drv_twi_tx(p_twi, address, &reg, 1, true);
    APP_ERROR_CHECK(err_code);
    err_code = nrf_drv_twi_rx(p_twi, address, res, 2);
    APP_ERROR_CHECK(err_code);

    return (uint16_t) ((res[1] << 8) | res[0]);
}

uint32_t veml6030_init(const nrf_drv_twi_t *l_twi)
{
    p_twi = l_twi;

    // Reset VEML configuration (in order to check device)
    return veml6030_write_reg(REG_ALS_CONF, 0);
}

uint32_t veml6030_power_on()
{
    // Get current config and clear shutdown bit
    uint16_t config = veml6030_read_reg(REG_ALS_CONF);
    config &= ~REG_ALS_CONF_SHUTDOWN;

    return veml6030_write_reg(REG_ALS_CONF, config);
}

uint32_t veml6030_shutdown()
{
    // Get current config and set shutdown bit
    uint16_t config = veml6030_read_reg(REG_ALS_CONF);
    config |= REG_ALS_CONF_SHUTDOWN;

    return veml6030_write_reg(REG_ALS_CONF, config);
}

uint32_t veml6030_set_als_integration_time(uint16_t it)
{
    uint16_t config = veml6030_read_reg(REG_ALS_CONF);
    config &= ~REG_ALS_CONF_IT_CLEAR;
    config |= it;
    return veml6030_write_reg(REG_ALS_CONF, config);
}

uint16_t veml6030_get_als_integration_time()
{
    uint16_t config = veml6030_read_reg(REG_ALS_CONF);
    return (config & REG_ALS_CONF_IT_CLEAR) >> 6;
}

uint32_t veml6030_set_als_gain(uint16_t gain)
{
    uint16_t config = veml6030_read_reg(REG_ALS_CONF);
    // Clear all gain bits
    config &= ~REG_ALS_CONF_GAIN_1_4;
    config |= gain;
    return veml6030_write_reg(REG_ALS_CONF, config);
}

uint16_t veml6030_get_als_gain()
{
    uint16_t config = veml6030_read_reg(REG_ALS_CONF);
    return (config & REG_ALS_CONF_GAIN_1_4) >> 11;
}
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
